M17-Project/TR-9/1.png

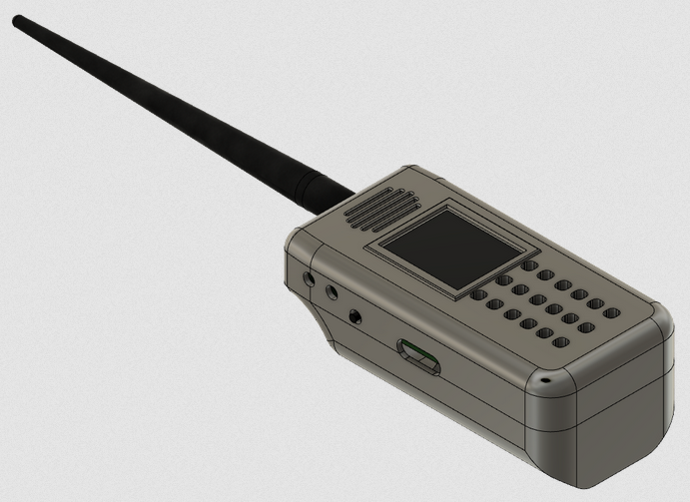
1.png
