M17-Project/TR-9/2.jpg

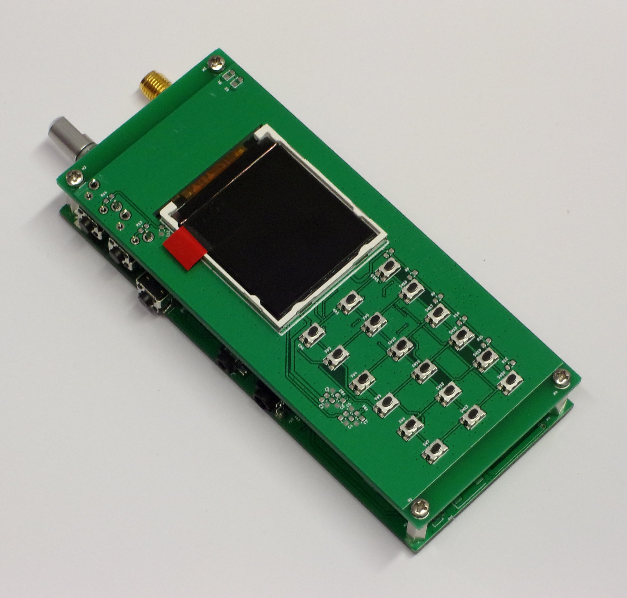
2.jpg
