M17-Project/TR-9/kicad/HMI/photo-1.png

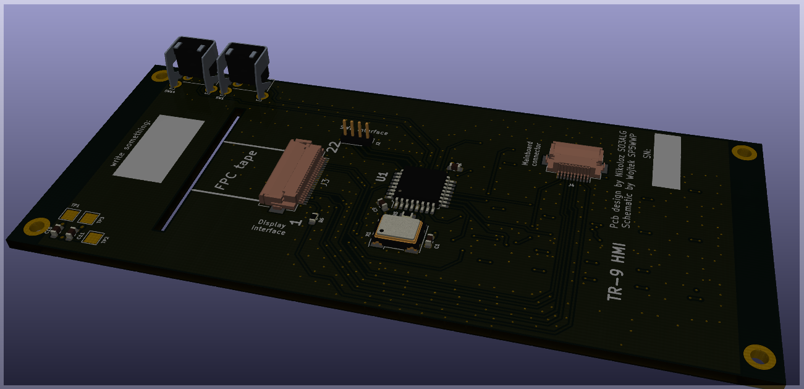
kicad/HMI/photo-1.png
