M17-Project/TR-9/kicad/HMI/photo-2.png

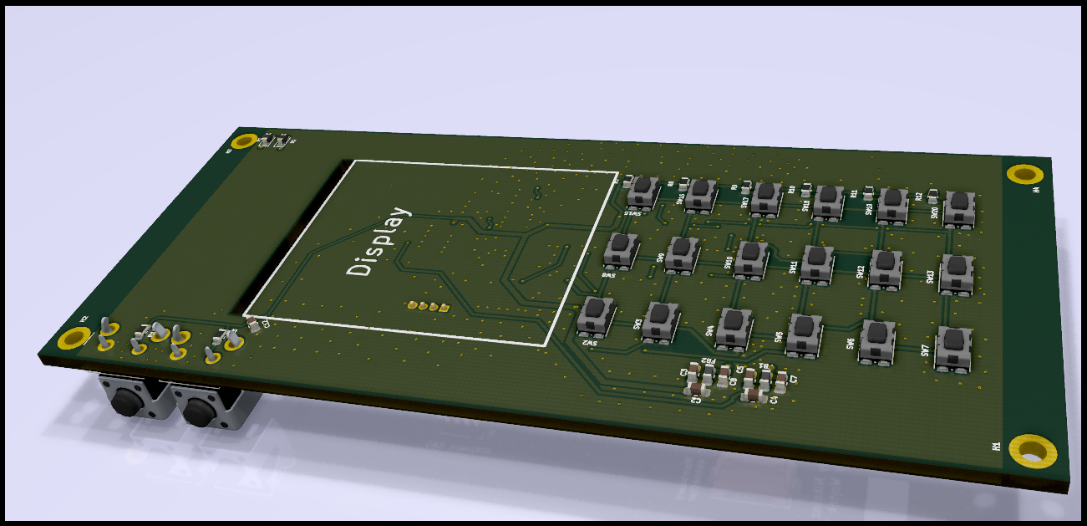
kicad/HMI/photo-2.png
