M17-Project/TR-9/kicad/HMI/photo-3.png

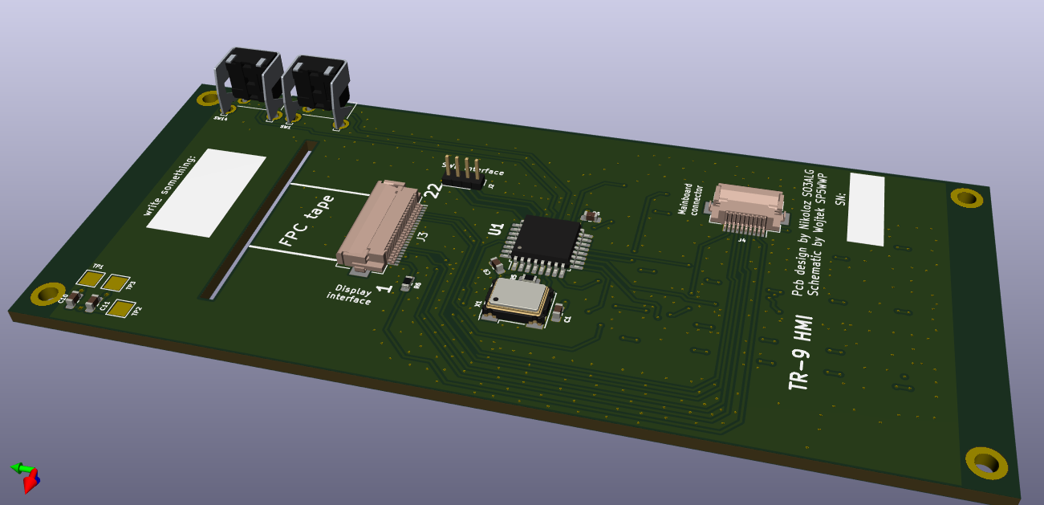
kicad/HMI/photo-3.png
