M17-Project/TR-9/kicad/HMI/photo-4.png

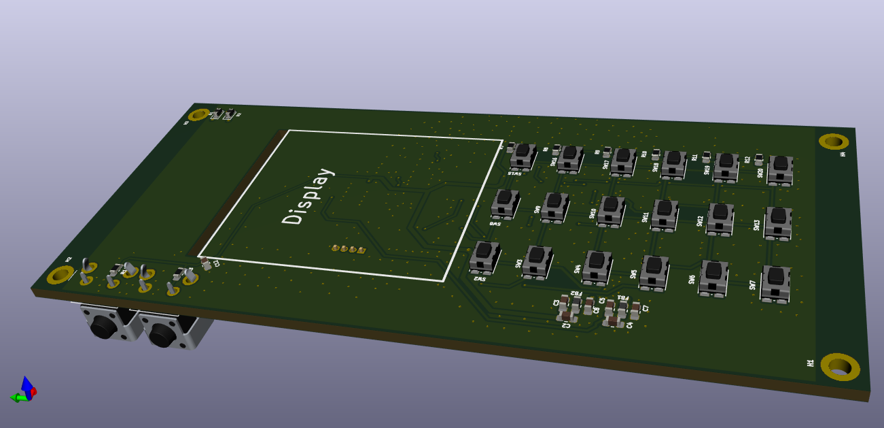
kicad/HMI/photo-4.png
