M17-Project/TR-9/kicad/Mainboard/photo-1.png

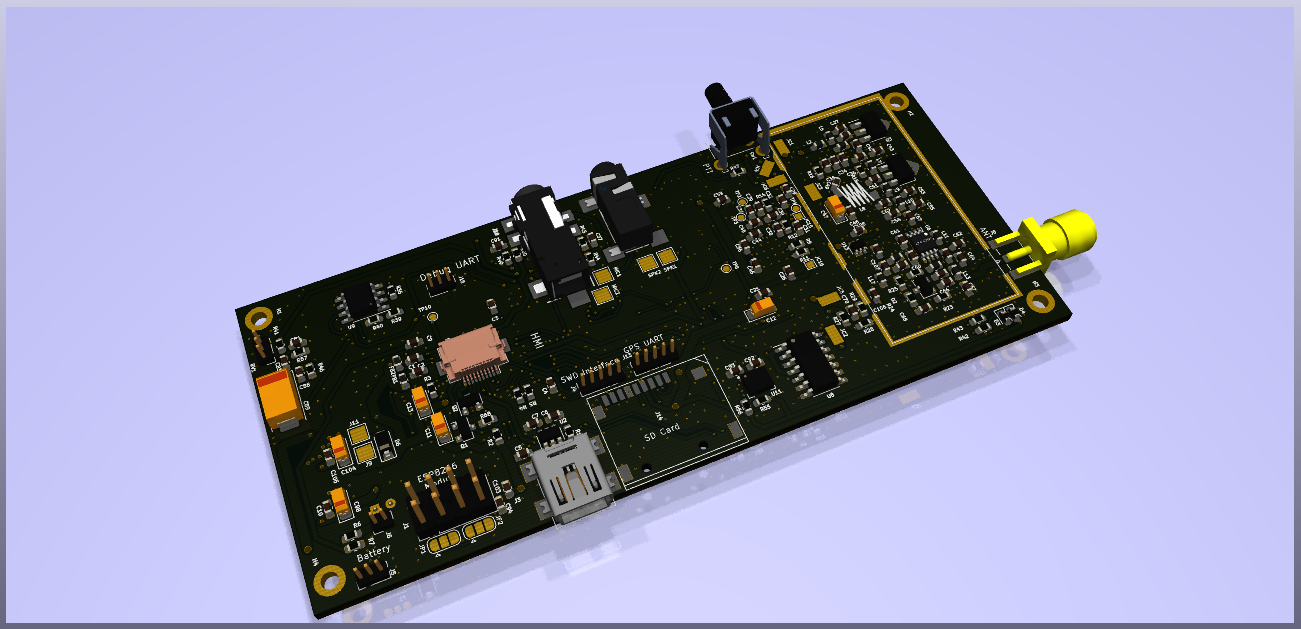
kicad/Mainboard/photo-1.png
