M17-Project/TR-9/kicad/Mainboard/photo-2.png

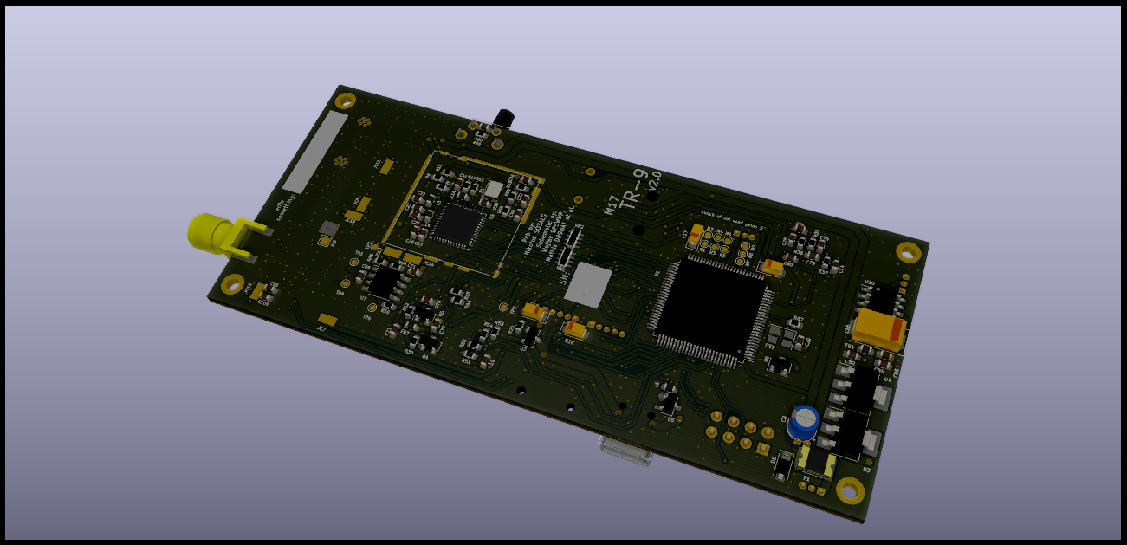
kicad/Mainboard/photo-2.png
