M17-Project/TR-9/kicad/Mainboard/photo-3.png

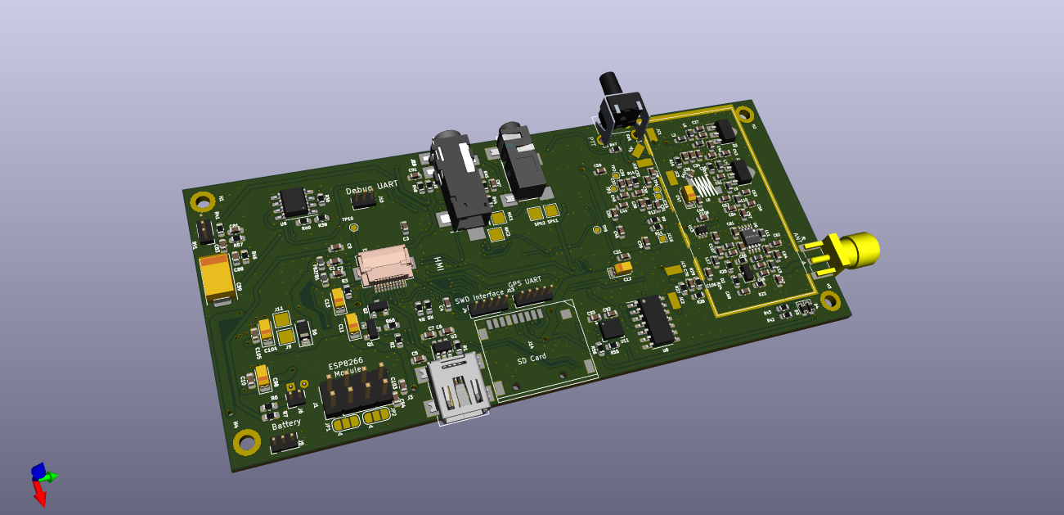
kicad/Mainboard/photo-3.png
