M17-Project/TR-9/kicad/Mainboard/photo-4.png

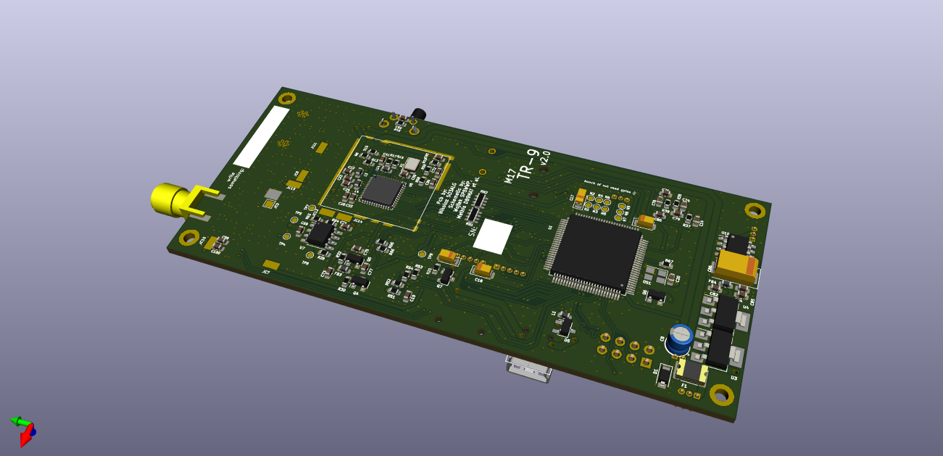
kicad/Mainboard/photo-4.png
