M17-Project/TR-9/cubemx/Inc/codeplug_auth.h

/*
 * codeplug_auth.h
 *
 *  Created on: 01.12.2018
 *      Author: SP5WWP
 */

#ifndef CODEPLUG_AUTH_H_
#define CODEPLUG_AUTH_H_

const uint8_t codeplug_auth_key[]={	0x77, 0x17, 0xd1, 0x12, 0xca, 0x7d, 0x91, 0x51,
									0x9d, 0x29, 0x99, 0x6b, 0x2b, 0x40, 0x33, 0xb9,
									0xb7, 0xc3, 0x41, 0x72, 0xb4, 0x95, 0x6b, 0x73,
									0x31, 0x1b, 0x98, 0x39, 0x0d, 0x82, 0xc7, 0xd5 };
const uint8_t codeplug_auth_iv[]={	0x28, 0xe9, 0xb2, 0xd3, 0x6e, 0x9c, 0xc2, 0x5e,
									0x92, 0x5b, 0xaa, 0xc6, 0x7a, 0xa7, 0xc3, 0x44 };

#define	CODEPLUG_AUTH_SUCCESS		0
#define	CODEPLUG_AUTH_FAIL			1

#endif /* CODEPLUG_AUTH_H_ */
