M17-Project/TR-9/cubemx/Inc/ecc_table.h

/*
 * ecc_table.h
 *
 *  Created on: 12.11.2018
 *      Author: SP5WWP
 */

#ifndef ECC_TABLE_H_
#define ECC_TABLE_H_

uint8_t ecc_16_8_table[256] = {	0x00, 0xB2, 0x65, 0xD7, 0xCA, 0x78, 0xAF, 0x1D, 0x95, 0x27, 0xF0, 0x42, 0x5F, 0xED, 0x3A, 0x88,
								0x2B, 0x99, 0x4E, 0xFC, 0xE1, 0x53, 0x84, 0x36, 0xBE, 0x0C, 0xDB, 0x69, 0x74, 0xC6, 0x11, 0xA3,
								0x56, 0xE4, 0x33, 0x81, 0x9C, 0x2E, 0xF9, 0x4B, 0xC3, 0x71, 0xA6, 0x14, 0x09, 0xBB, 0x6C, 0xDE,
								0x7D, 0xCF, 0x18, 0xAA, 0xB7, 0x05, 0xD2, 0x60, 0xE8, 0x5A, 0x8D, 0x3F, 0x22, 0x90, 0x47, 0xF5,
								0xAC, 0x1E, 0xC9, 0x7B, 0x66, 0xD4, 0x03, 0xB1, 0x39, 0x8B, 0x5C, 0xEE, 0xF3, 0x41, 0x96, 0x24,
								0x87, 0x35, 0xE2, 0x50, 0x4D, 0xFF, 0x28, 0x9A, 0x12, 0xA0, 0x77, 0xC5, 0xD8, 0x6A, 0xBD, 0x0F,
								0xFA, 0x48, 0x9F, 0x2D, 0x30, 0x82, 0x55, 0xE7, 0x6F, 0xDD, 0x0A, 0xB8, 0xA5, 0x17, 0xC0, 0x72,
								0xD1, 0x63, 0xB4, 0x06, 0x1B, 0xA9, 0x7E, 0xCC, 0x44, 0xF6, 0x21, 0x93, 0x8E, 0x3C, 0xEB, 0x59,
								0x59, 0xEB, 0x3C, 0x8E, 0x93, 0x21, 0xF6, 0x44, 0xCC, 0x7E, 0xA9, 0x1B, 0x06, 0xB4, 0x63, 0xD1,
								0x72, 0xC0, 0x17, 0xA5, 0xB8, 0x0A, 0xDD, 0x6F, 0xE7, 0x55, 0x82, 0x30, 0x2D, 0x9F, 0x48, 0xFA,
								0x0F, 0xBD, 0x6A, 0xD8, 0xC5, 0x77, 0xA0, 0x12, 0x9A, 0x28, 0xFF, 0x4D, 0x50, 0xE2, 0x35, 0x87,
								0x24, 0x96, 0x41, 0xF3, 0xEE, 0x5C, 0x8B, 0x39, 0xB1, 0x03, 0xD4, 0x66, 0x7B, 0xC9, 0x1E, 0xAC,
								0xF5, 0x47, 0x90, 0x22, 0x3F, 0x8D, 0x5A, 0xE8, 0x60, 0xD2, 0x05, 0xB7, 0xAA, 0x18, 0xCF, 0x7D,
								0xDE, 0x6C, 0xBB, 0x09, 0x14, 0xA6, 0x71, 0xC3, 0x4B, 0xF9, 0x2E, 0x9C, 0x81, 0x33, 0xE4, 0x56,
								0xA3, 0x11, 0xC6, 0x74, 0x69, 0xDB, 0x0C, 0xBE, 0x36, 0x84, 0x53, 0xE1, 0xFC, 0x4E, 0x99, 0x2B,
								0x88, 0x3A, 0xED, 0x5F, 0x42, 0xF0, 0x27, 0x95, 0x1D, 0xAF, 0x78, 0xCA, 0xD7, 0x65, 0xB2, 0x00 };

#endif /* ECC_TABLE_H_ */
