M17-Project/TR-9/cubemx/Inc/fields.h

/*
 * fields.h
 *
 *  Created on: 20.11.2018
 *      Author: SP5WWP
 */

#ifndef FIELDS_H_
#define FIELDS_H_

#define		CONTENT_VOICE				1
#define		CONTENT_DATA				2
#define		CONTENT_VOICE_DATA			3

#define		ENC_NONE					0
#define		ENC_STATIC_KEY				1
#define		ENC_DYNAMIC_KEY				2

#define		GPS_NONE					0

#define		KEY_NONE					0

#define		TALKGROUP_NONE				0

#endif /* FIELDS_H_ */
